Waddle-Penguin/Penguin_Paddle/Images/Learning Experiences with GitHub.png

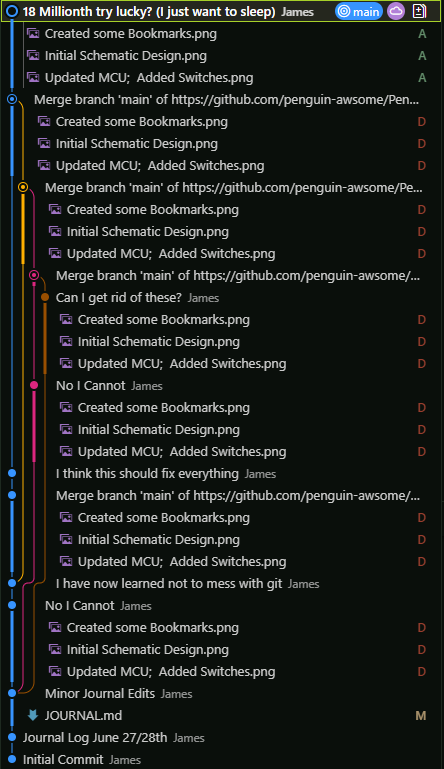
Images/Learning Experiences with GitHub.png
