Waddle-Penguin/Penguin_Paddle/Images/README Images/IMG_4678.png

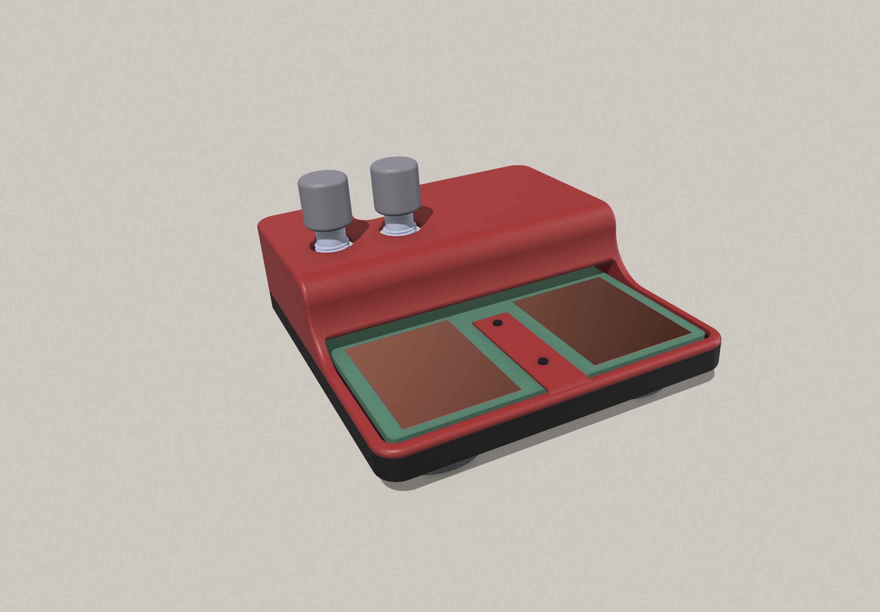
Images/README Images/IMG_4678.png
