Waddle-Penguin/Penguin_Paddle/Images/README Images/IMG_4679.png

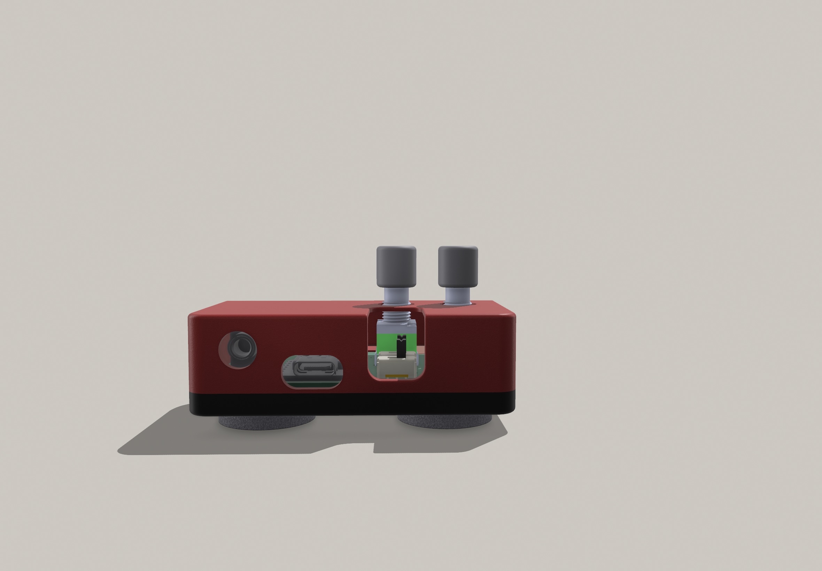
Images/README Images/IMG_4679.png
