Waddle-Penguin/Penguin_Paddle/Images/README Images/IMG_4680.png

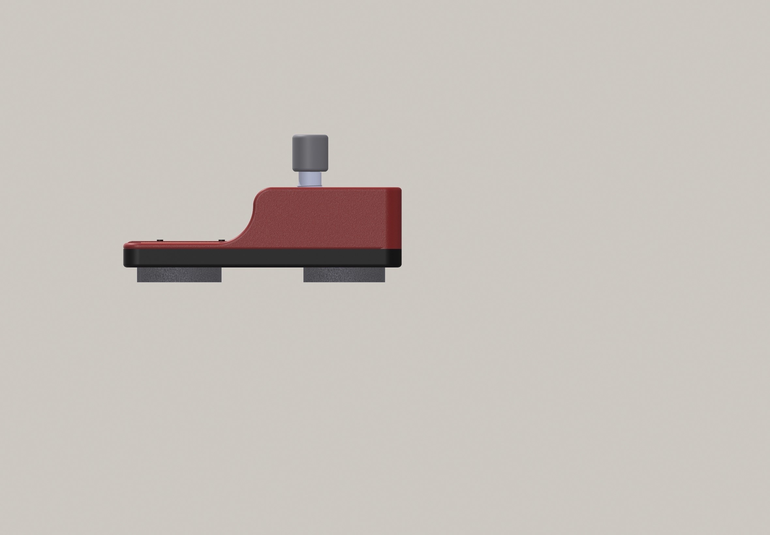
Images/README Images/IMG_4680.png
