Waddle-Penguin/Penguin_Paddle/Images/README Images/Screenshot 2025-07-03 001631.png

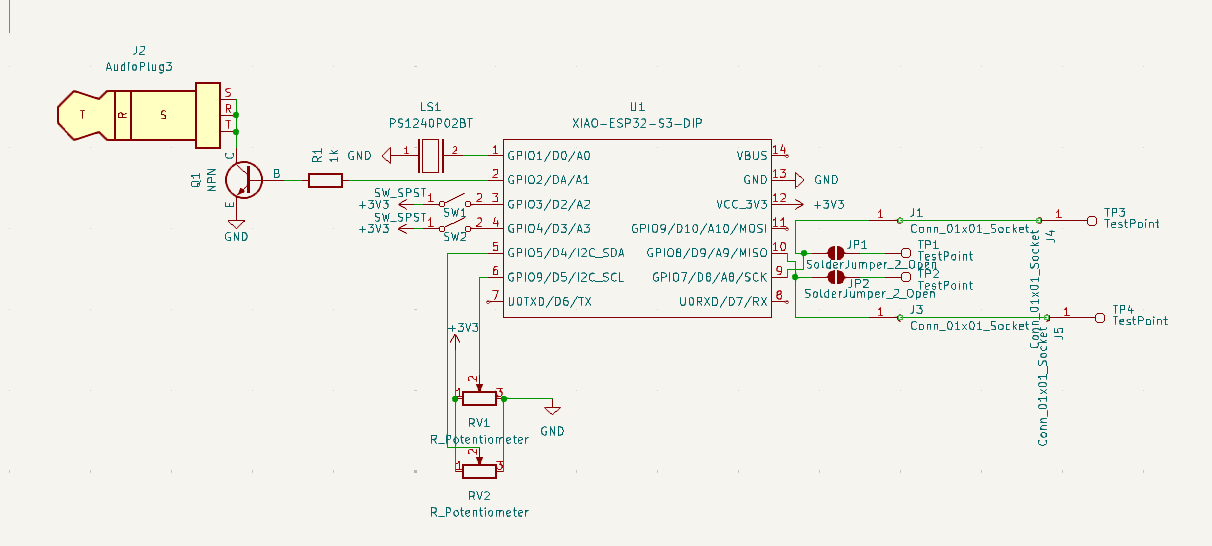
Images/README Images/Screenshot 2025-07-03 001631.png
