Waddle-Penguin/Penguin_Paddle/Images/Screenshot 2025-06-28 133224.png

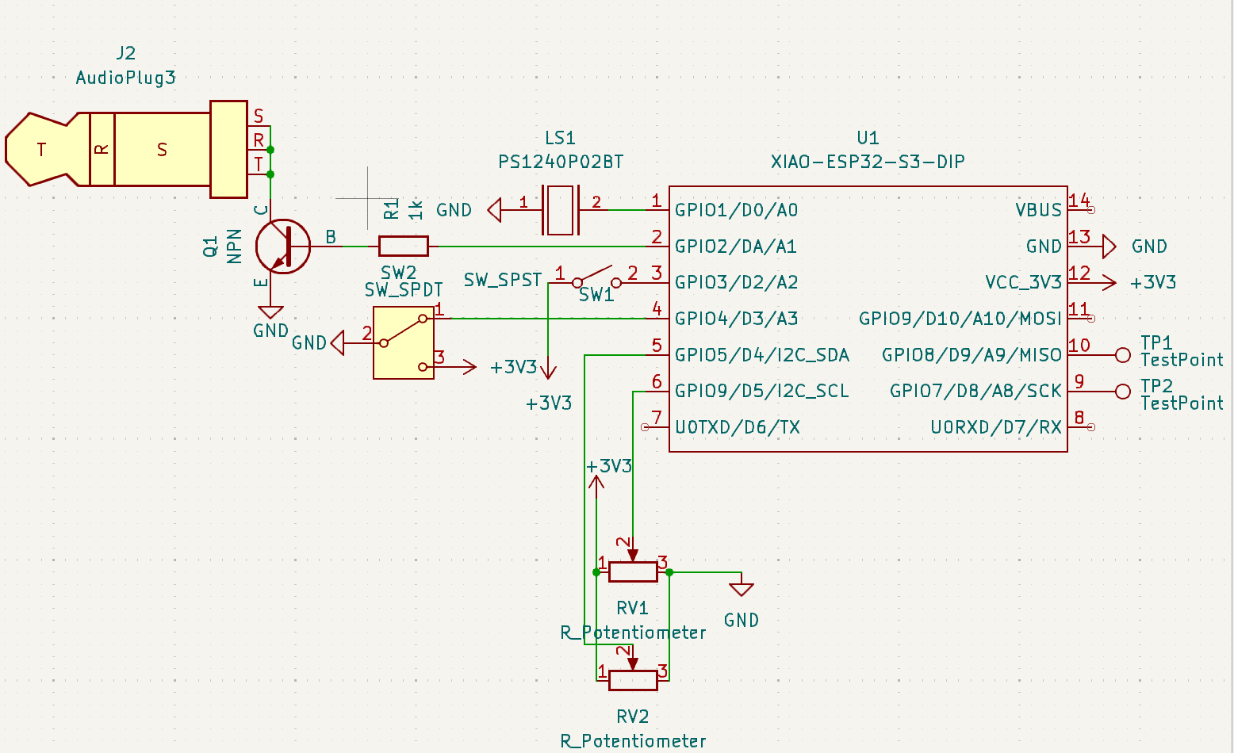
Images/Screenshot 2025-06-28 133224.png
