Waddle-Penguin/Penguin_Paddle/Images/Screenshot 2025-06-28 143728.png

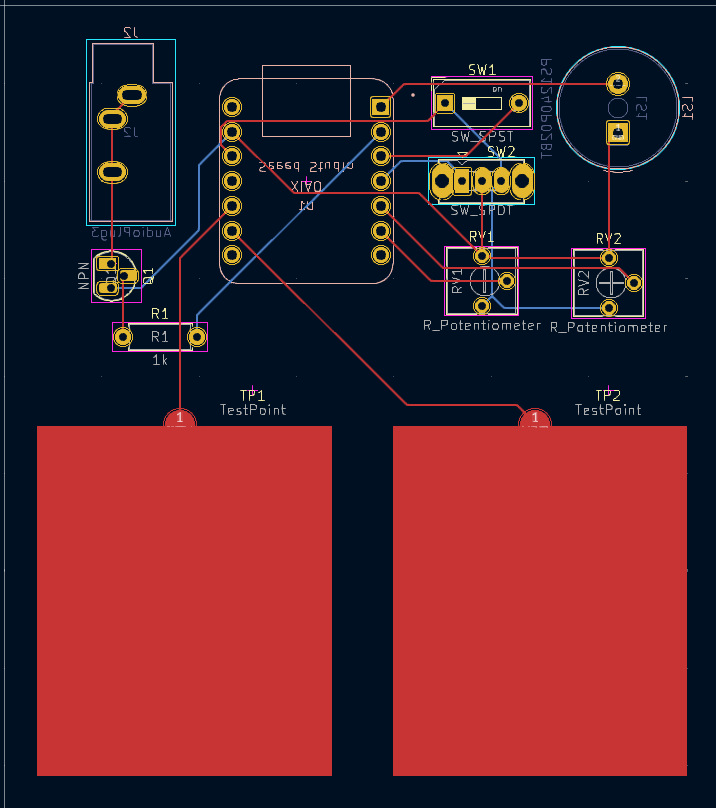
Images/Screenshot 2025-06-28 143728.png
