Waddle-Penguin/Penguin_Paddle/Images/Screenshot 2025-06-29 010514.png

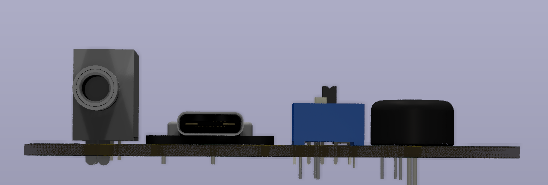
Images/Screenshot 2025-06-29 010514.png
