Waddle-Penguin/Penguin_Paddle/Images/Screenshot 2025-06-29 162933.png

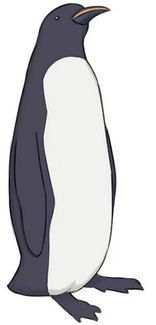
Images/Screenshot 2025-06-29 162933.png
