Waddle-Penguin/Penguin_Paddle/Images/Screenshot 2025-06-29 225659.png

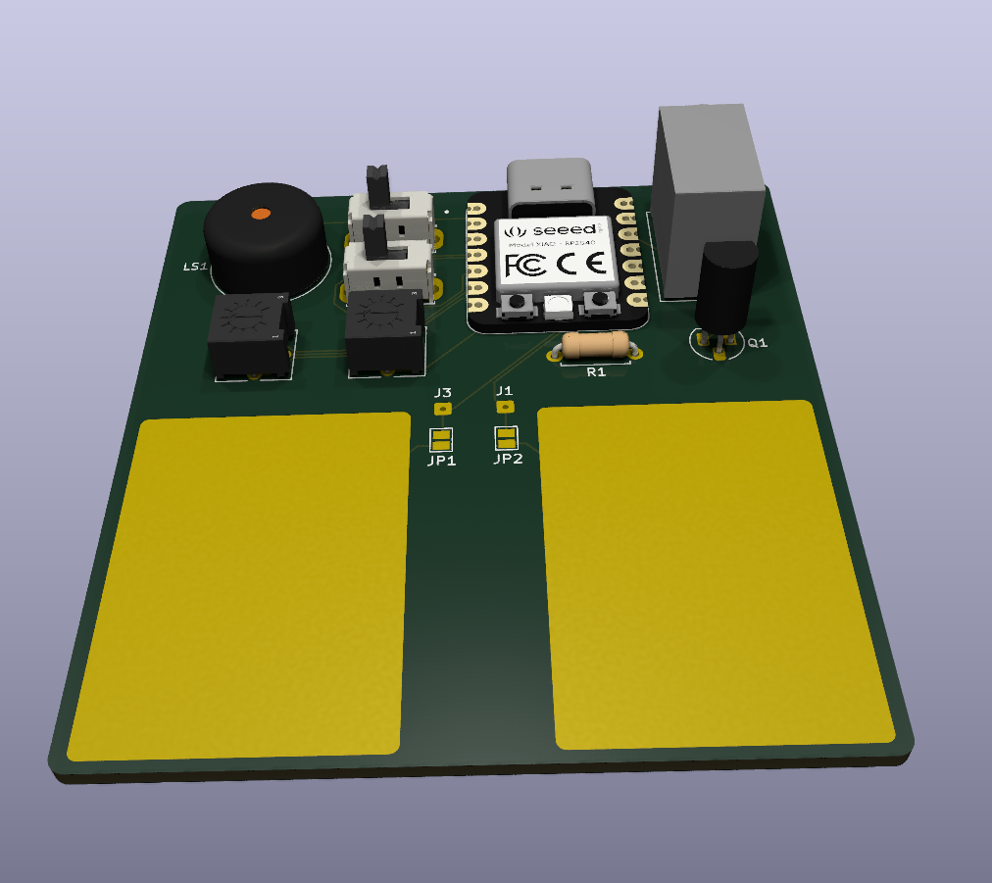
Images/Screenshot 2025-06-29 225659.png
