Waddle-Penguin/Penguin_Paddle/Images/Screenshot 2025-07-01 024233.png

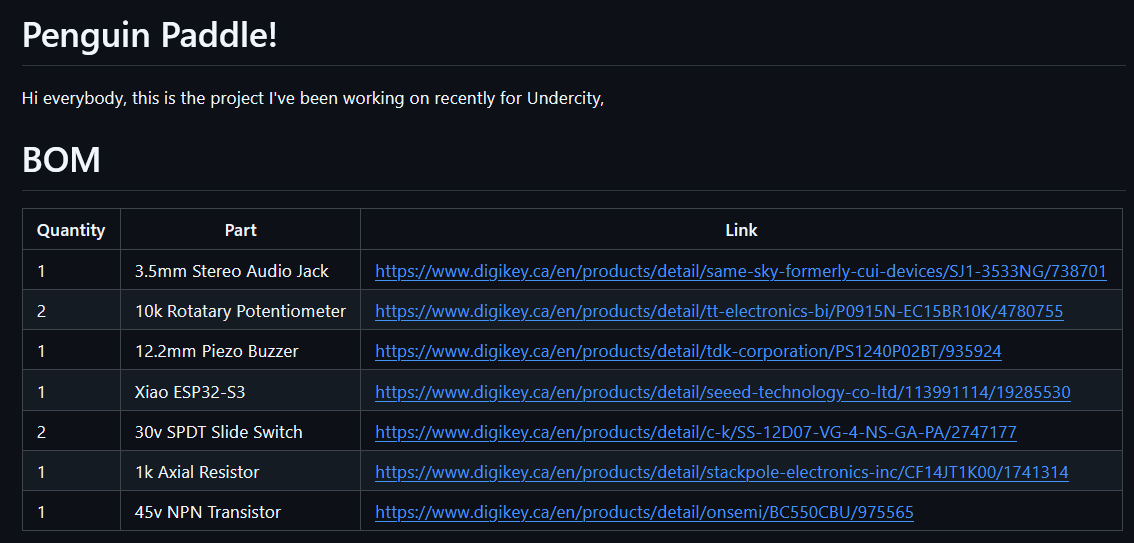
Images/Screenshot 2025-07-01 024233.png
